m112521/useless-machines/imgs/a4988.jpeg

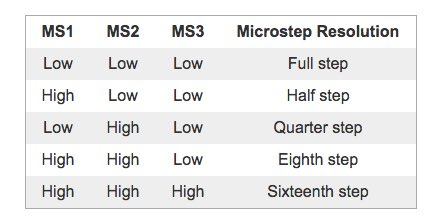
imgs/a4988.jpeg
