m112521/useless-machines/imgs/microstep-config.jpg

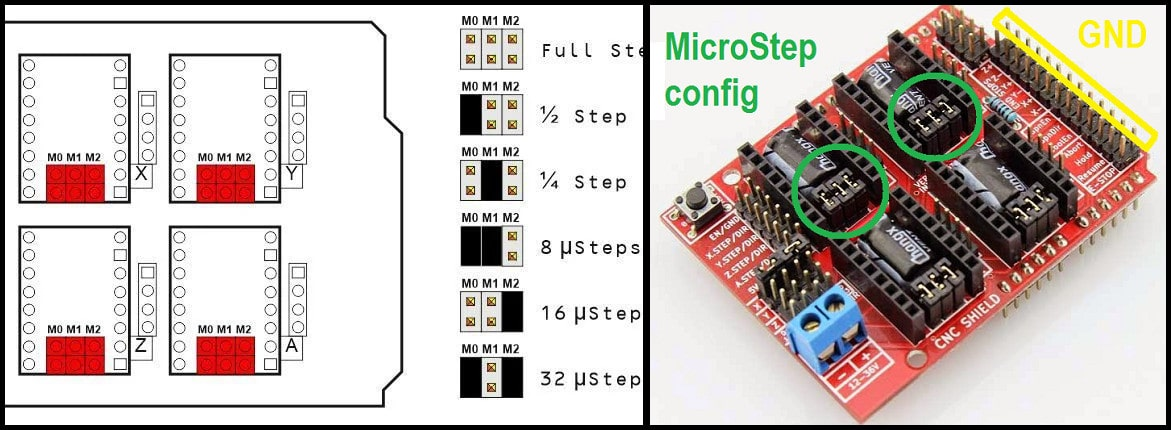
imgs/microstep-config.jpg
