m112521/useless-machines/STL/Z-axis/ToolHolder_v01.stl

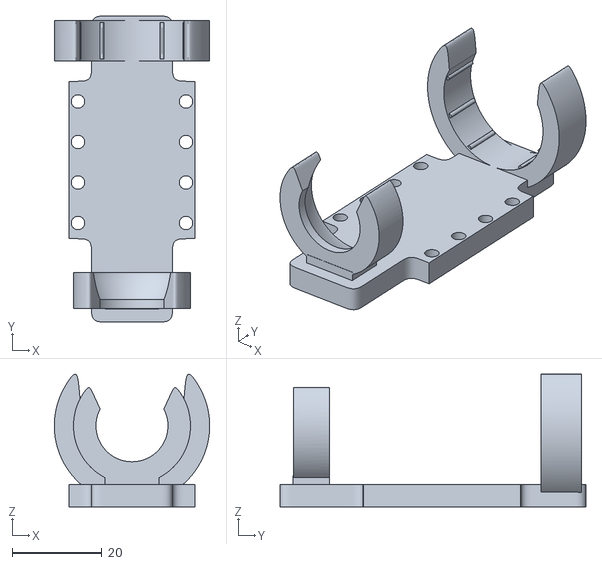
[picture p21: CAD file, 2024-03-12]
STL/Z-axis/ToolHolder_v01.stl
34.5 x 68.0 x 29.5
