m112521/useless-machines/CAD/baseD3.dxf

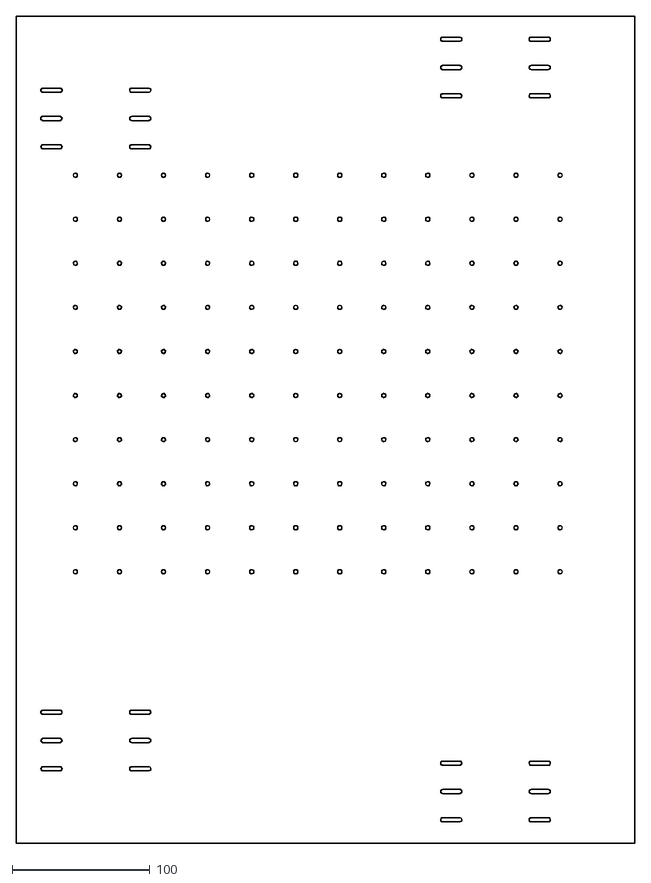
[picture p22: CAD file, 2024-06-20]
CAD/baseD3.dxf
449.3 x 600.6
