m112521/useless-machines/KIT/racks.dxf

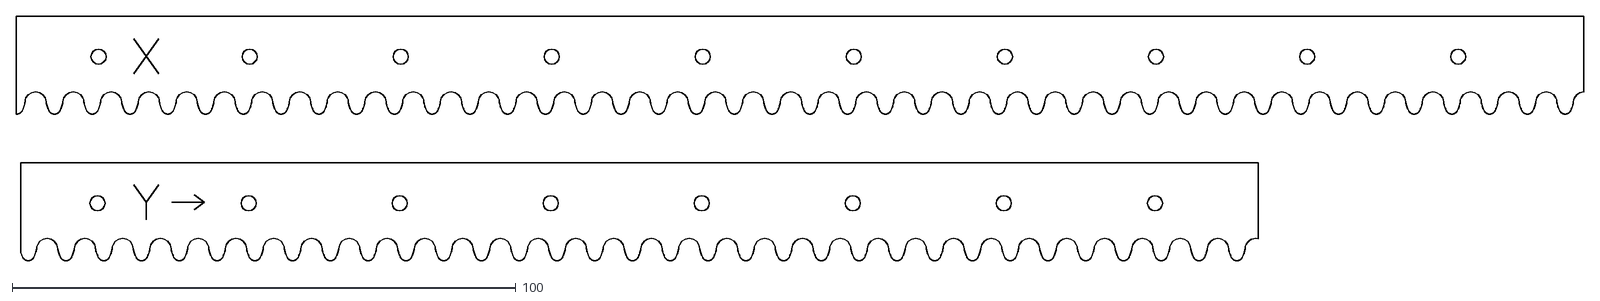
[picture p23: CAD file, 2024-05-28]
KIT/racks.dxf
311.4 x 48.5
