m112521/useless-machines/STEP/carrige_bread_t18_w50.stp

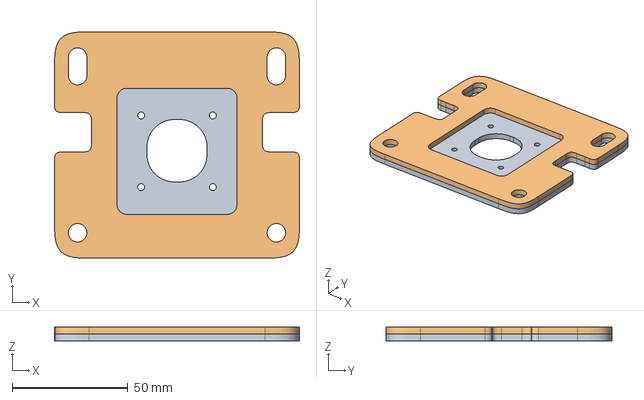
[picture p24: CAD file, 2026-01-15]
STEP/carrige_bread_t18_w50.stp
106.0 x 97.9 x 6.00 mm
