m112521/useless-machines/STL/endstopHolderVX.stl

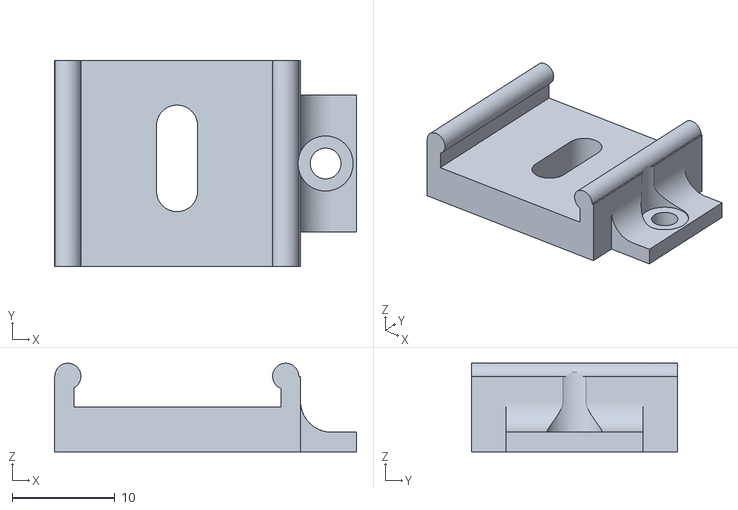
[picture p25: CAD file, 2024-07-02]
STL/endstopHolderVX.stl
29.3 x 20.0 x 8.61
