m112521/useless-machines/STL/Z-axis/StepperHolders.stl

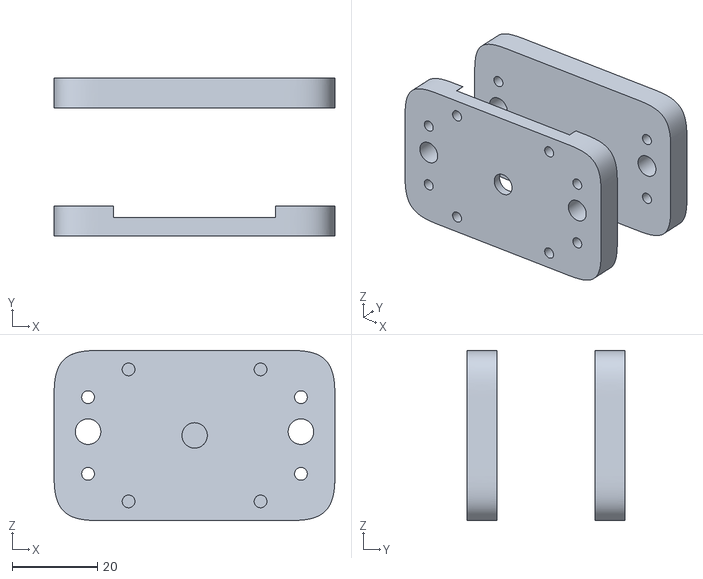
[picture p26: CAD file, 2024-03-07]
STL/Z-axis/StepperHolders.stl
66.0 x 37.0 x 40.0
