m112521/useless-machines/CAD/baseD6.dxf

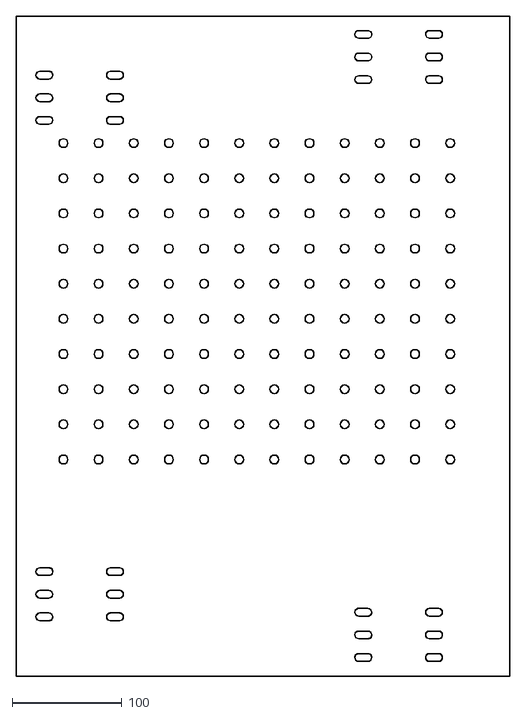
[picture p27: CAD file, 2024-06-20]
CAD/baseD6.dxf
449.3 x 600.6
