m112521/useless-machines/STEP/carrige_cheese_t12_w50.stp

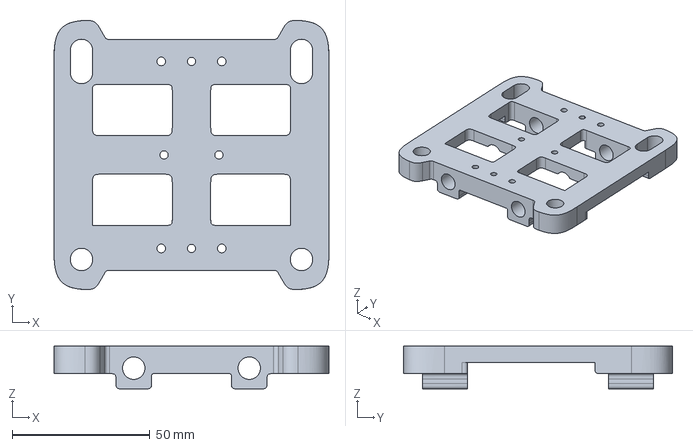
[picture p28: CAD file, 2026-01-15]
STEP/carrige_cheese_t12_w50.stp
100.0 x 97.9 x 15.5 mm
