m112521/useless-machines/STL/endstopHolder_v2.stl

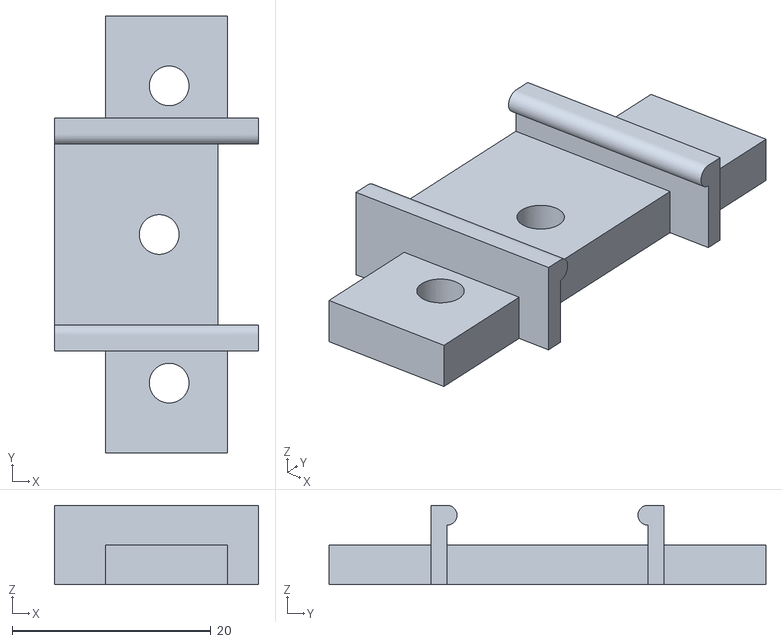
[picture p29: CAD file, 2024-06-11]
STL/endstopHolder_v2.stl
20.5 x 44.0 x 8.00
