m112521/useless-machines/CAD/cameraBeam.dxf

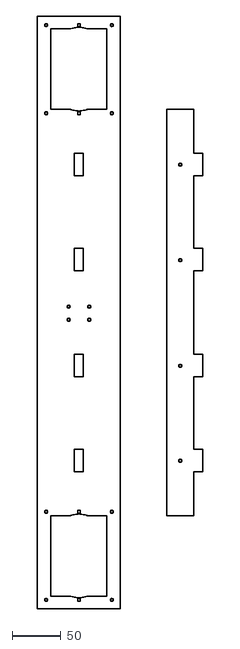
[picture p30: CAD file, 2024-06-07]
CAD/cameraBeam.dxf
169.0 x 605.0
