m112521/useless-machines/STL/foot.stl

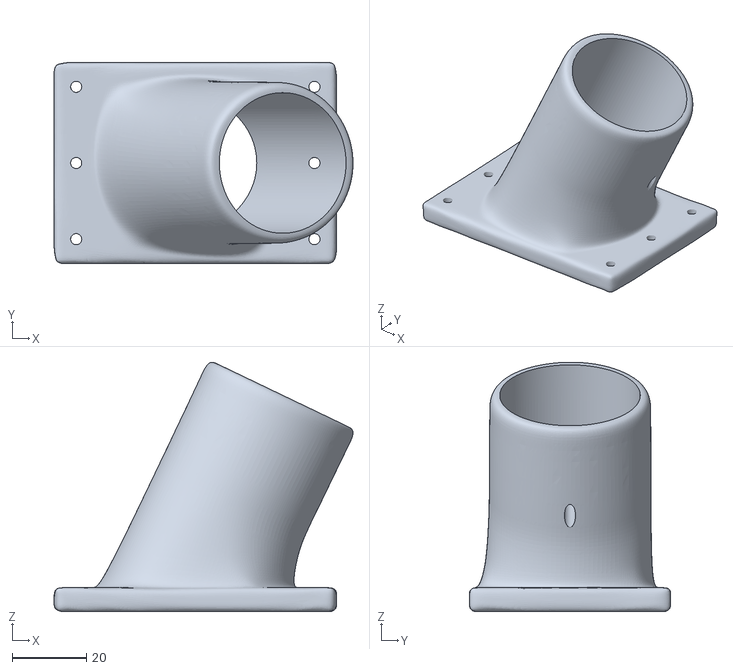
[picture p32: CAD file, 2024-05-28]
STL/foot.stl
80.8 x 54.4 x 67.4
