m112521/useless-machines/STL/Z-axis/RailHolderTop.stl

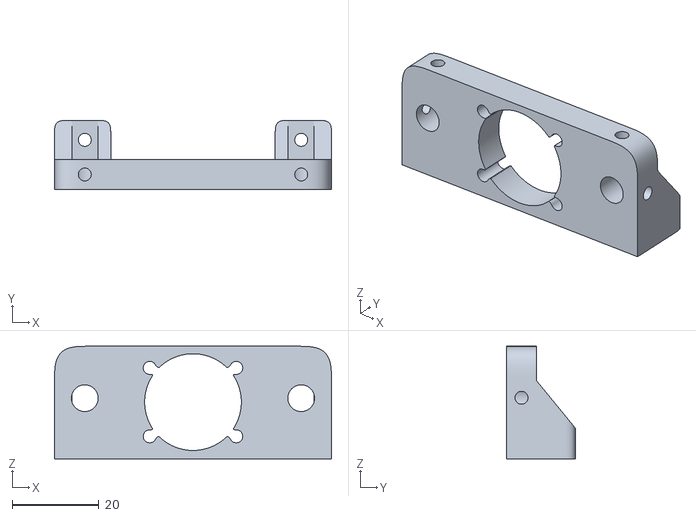
[picture p33: CAD file, 2024-03-01]
STL/Z-axis/RailHolderTop.stl
64.0 x 16.0 x 26.0
