m112521/useless-machines/CAD/flexicamRail.dxf

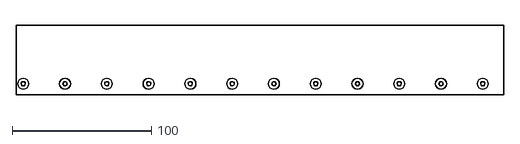
[picture p34: CAD file, 2023-10-10]
CAD/flexicamRail.dxf
350.0 x 50.0
