m112521/useless-machines/STEP/carrige_cheese_t18_w50.stp

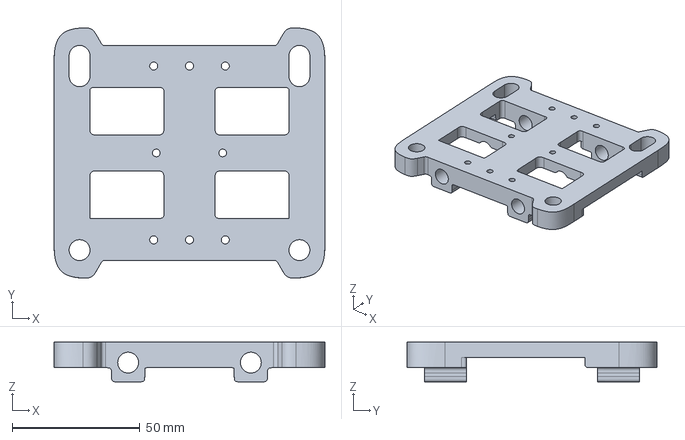
[picture p35: CAD file, 2026-01-15]
STEP/carrige_cheese_t18_w50.stp
106.0 x 97.9 x 15.5 mm
