m112521/useless-machines/STL/axisSupport_v2.stl

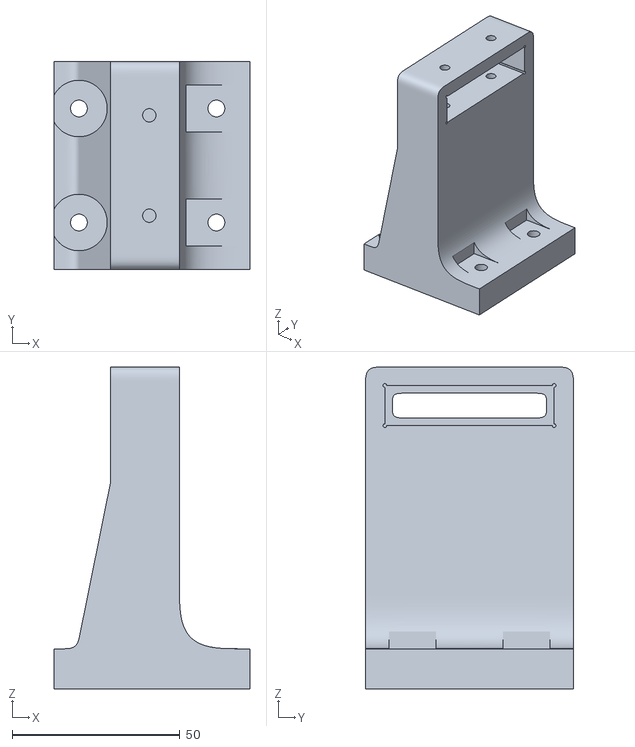
[picture p36: CAD file, 2024-04-23]
STL/axisSupport_v2.stl
58.4 x 62.0 x 96.0
