m112521/useless-machines/STL/Z-axis/Plate.stl

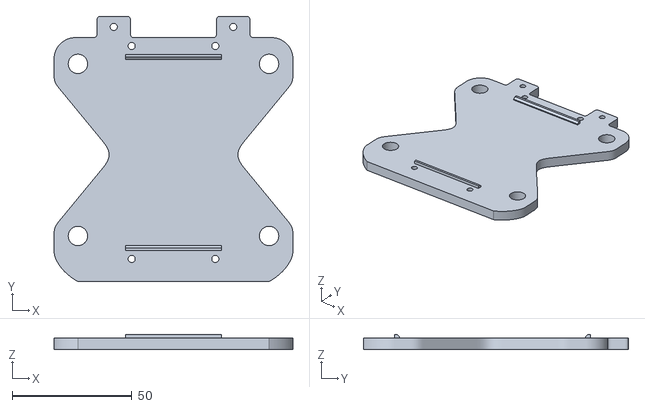
[picture p37: CAD file, 2024-03-01]
STL/Z-axis/Plate.stl
100.0 x 111.0 x 6.48
