m112521/useless-machines/STEP/carrige_endstopHolder.stp

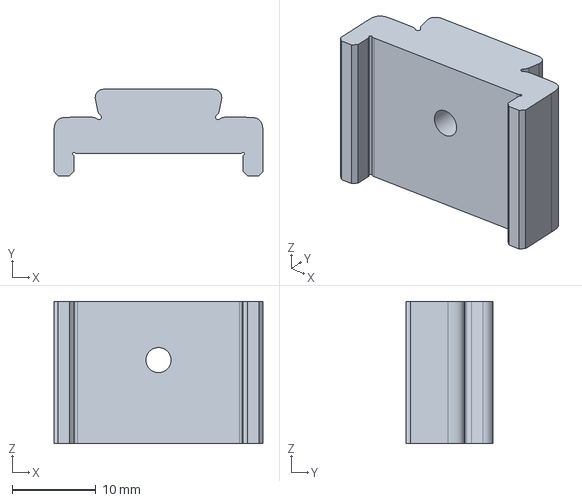
[picture p38: CAD file, 2026-01-15]
STEP/carrige_endstopHolder.stp
25.0 x 10.3 x 17.0 mm
