m112521/useless-machines/STL/bottomBearingSpacers_v2.stl

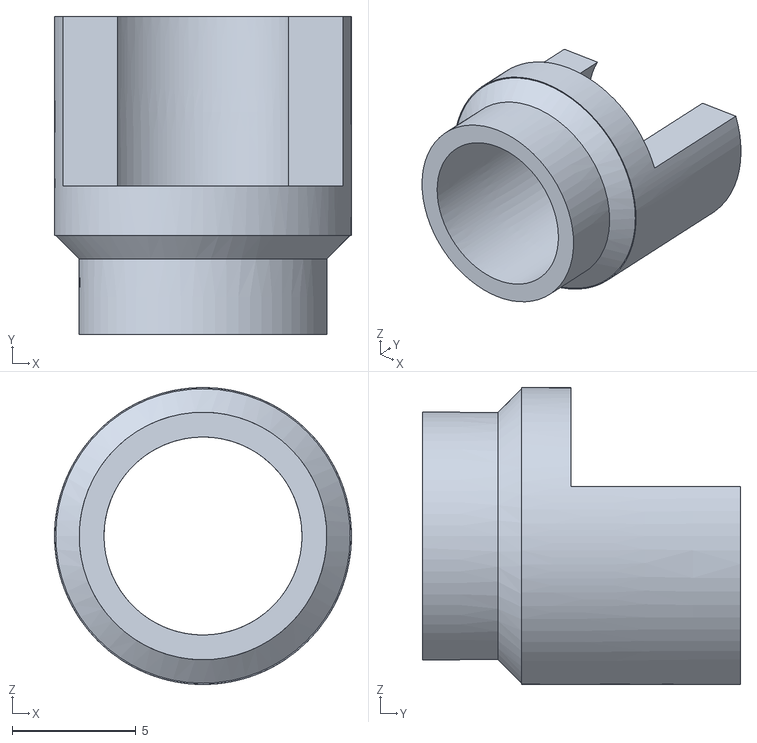
[picture p39: CAD file, 2024-04-23]
STL/bottomBearingSpacers_v2.stl
12.0 x 12.9 x 12.0
