m112521/useless-machines/STL/Z-axis/RailHolderBottom.stl

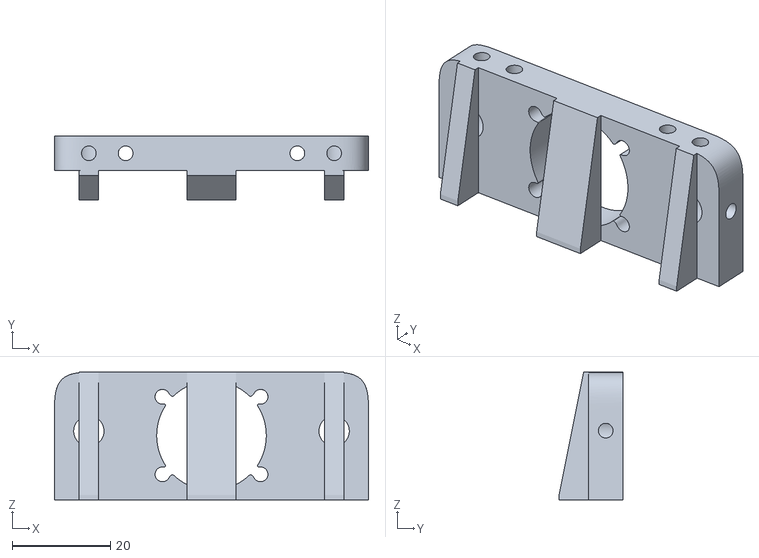
[picture p40: CAD file, 2024-03-01]
STL/Z-axis/RailHolderBottom.stl
64.0 x 13.0 x 26.0
