m112521/useless-machines/STEP/carrige_jam_t18_w50.stp

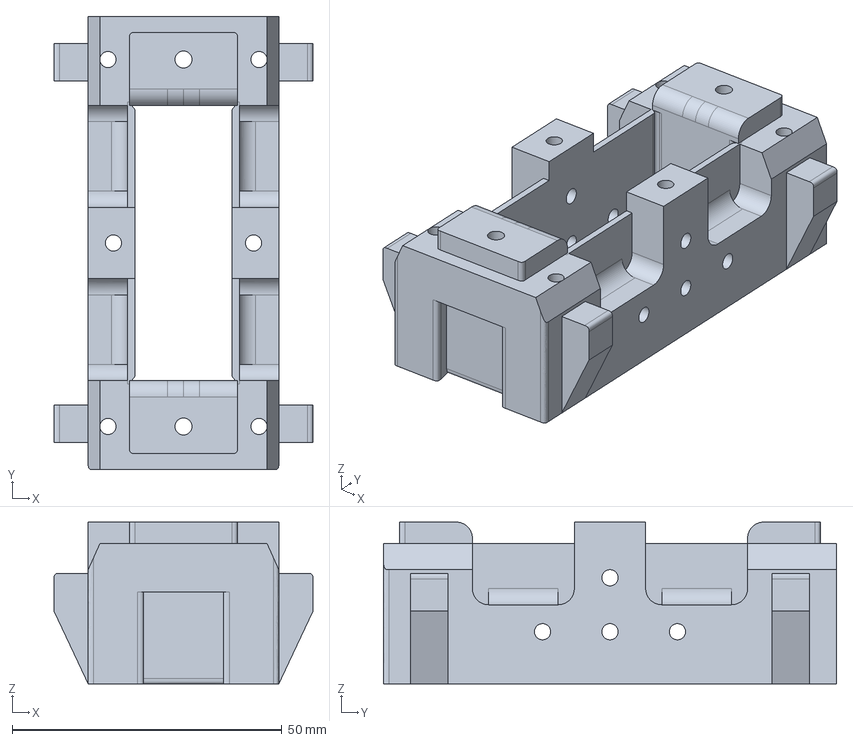
[picture p41: CAD file, 2026-01-15]
STEP/carrige_jam_t18_w50.stp
48.0 x 84.0 x 30.0 mm
