m112521/useless-machines/STL/bearingSpacer.stl

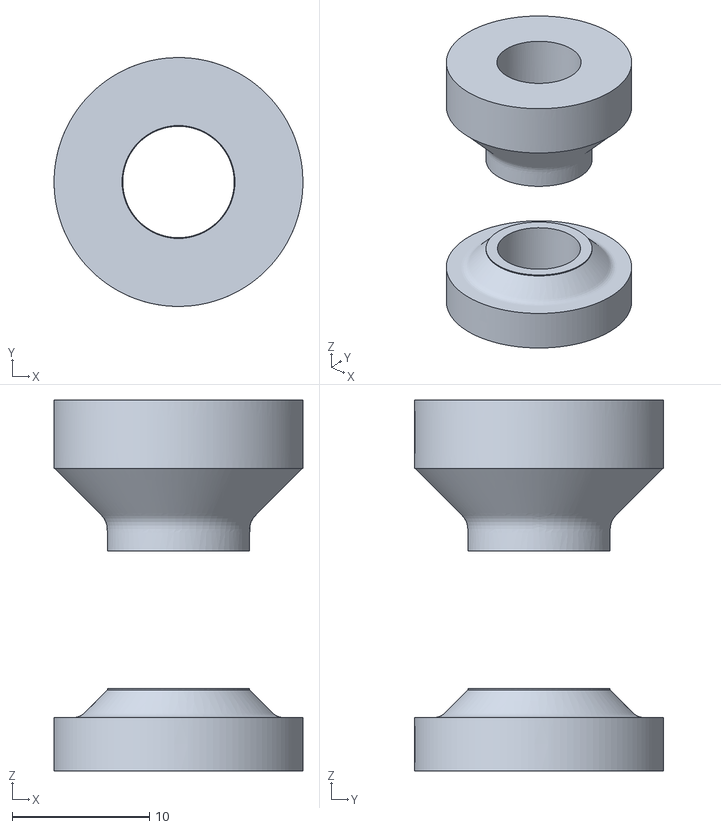
[picture p42: CAD file, 2023-11-07]
STL/bearingSpacer.stl
18.1 x 18.1 x 27.0
