m112521/useless-machines/STL/Z-axis/RailHolderTop_spacered.stl

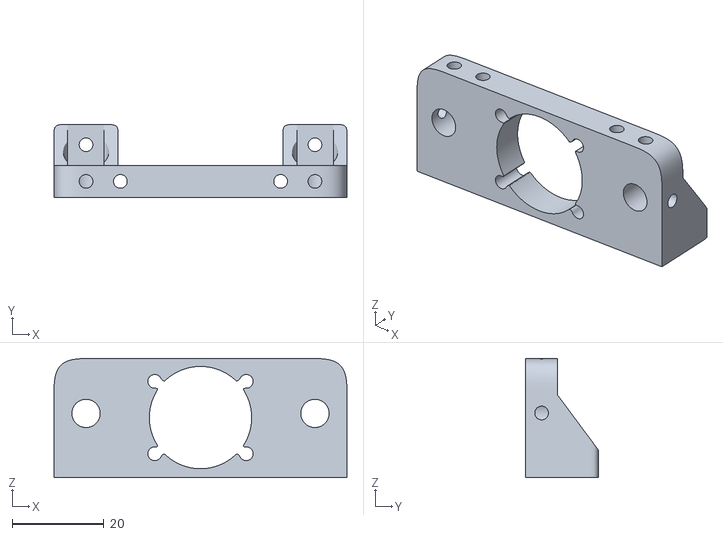
[picture p43: CAD file, 2024-03-01]
STL/Z-axis/RailHolderTop_spacered.stl
64.0 x 15.9 x 26.0
