m112521/useless-machines/STL/pinion.stl

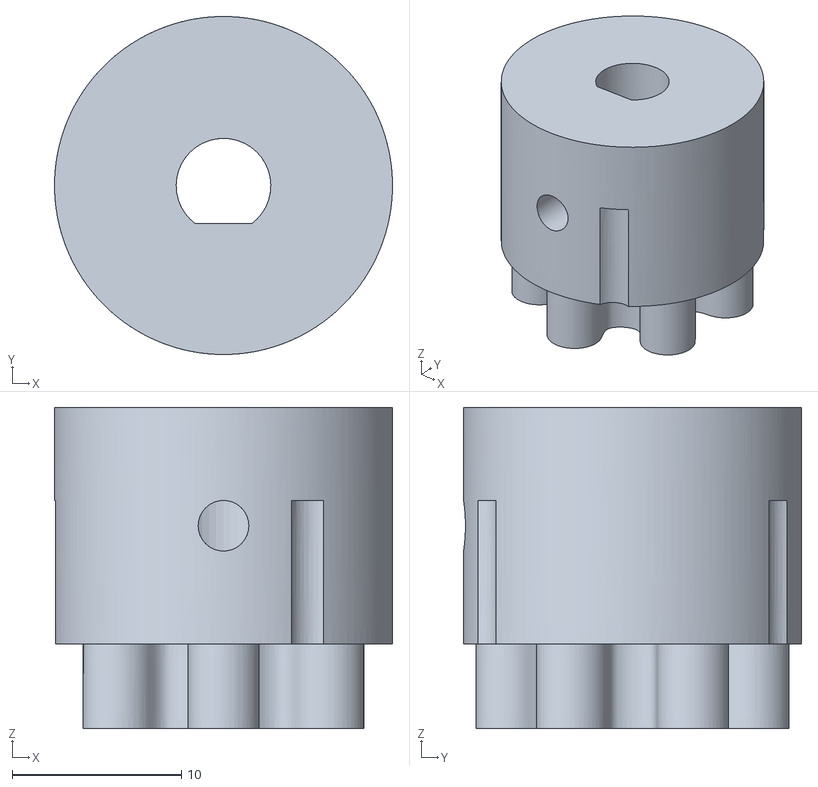
[picture p44: CAD file, 2023-11-07]
STL/pinion.stl
20.0 x 20.0 x 19.0
