m112521/useless-machines/STL/axisSupportStatic.stl

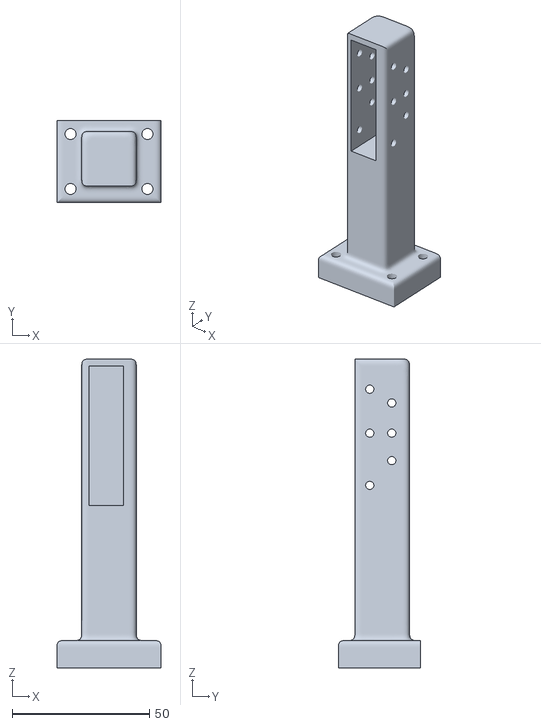
[picture p45: CAD file, 2023-11-07]
STL/axisSupportStatic.stl
38.0 x 30.0 x 112.5
