m112521/useless-machines/STL/perpAxisHolderArched.stl

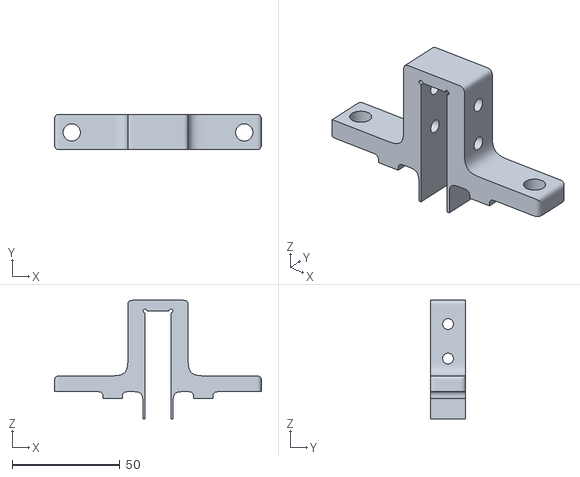
[picture p46: CAD file, 2023-11-07]
STL/perpAxisHolderArched.stl
96.0 x 16.4 x 55.0
