m112521/useless-machines/STL/carrigeBracket.stl

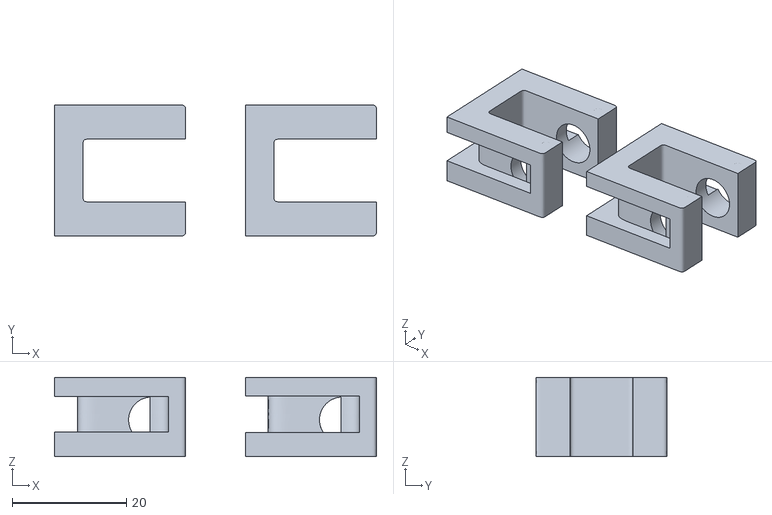
[picture p47: CAD file, 2023-10-10]
STL/carrigeBracket.stl
56.5 x 23.0 x 13.9
