m112521/useless-machines/STL/BottomCarrigePLA2.stl

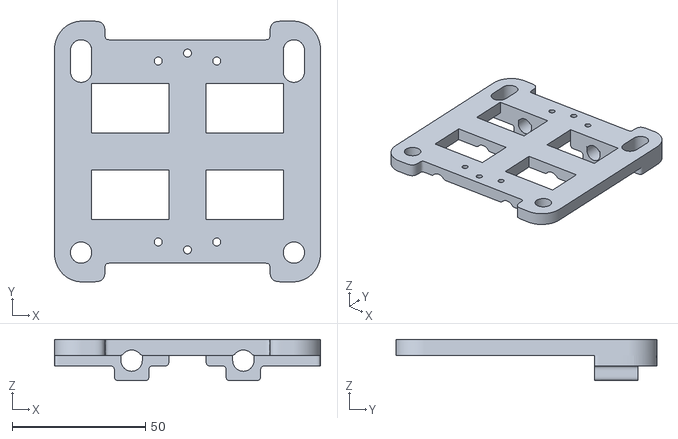
[picture p48: CAD file, 2023-10-10]
STL/BottomCarrigePLA2.stl
100.0 x 98.0 x 15.5
