m112521/useless-machines/STL/nemaHolder.stl

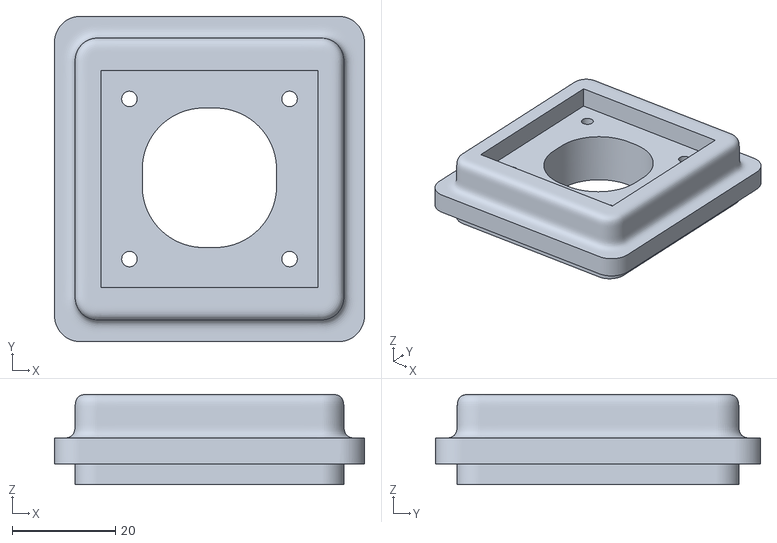
[picture p49: CAD file, 2023-10-10]
STL/nemaHolder.stl
60.0 x 62.9 x 17.5
