m112521/useless-machines/STL/BottomCarrigePLA3.stl

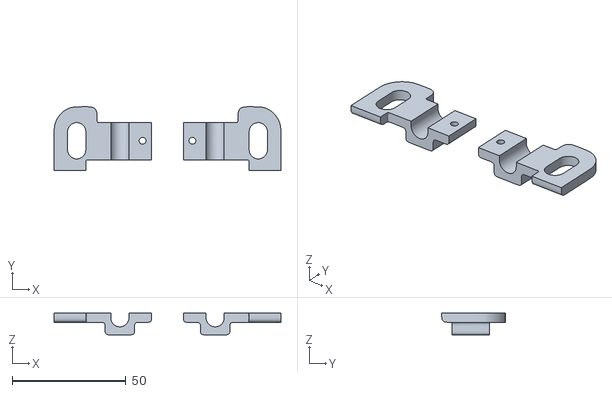
[picture p50: CAD file, 2023-10-10]
STL/BottomCarrigePLA3.stl
100.0 x 28.0 x 9.52
