m112521/useless-machines/STL/BottomCarrigePLA.stl

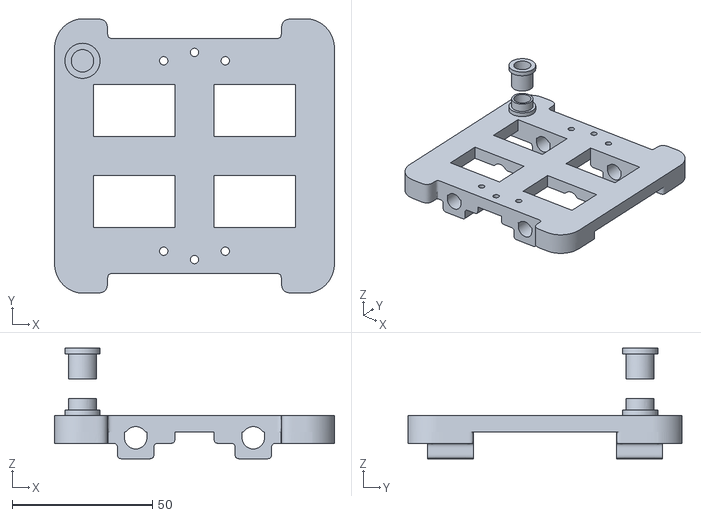
[picture p51: CAD file, 2023-10-10]
STL/BottomCarrigePLA.stl
100.0 x 98.0 x 39.5
