m112521/useless-machines/imgs/diodeLaser-setup.jpg

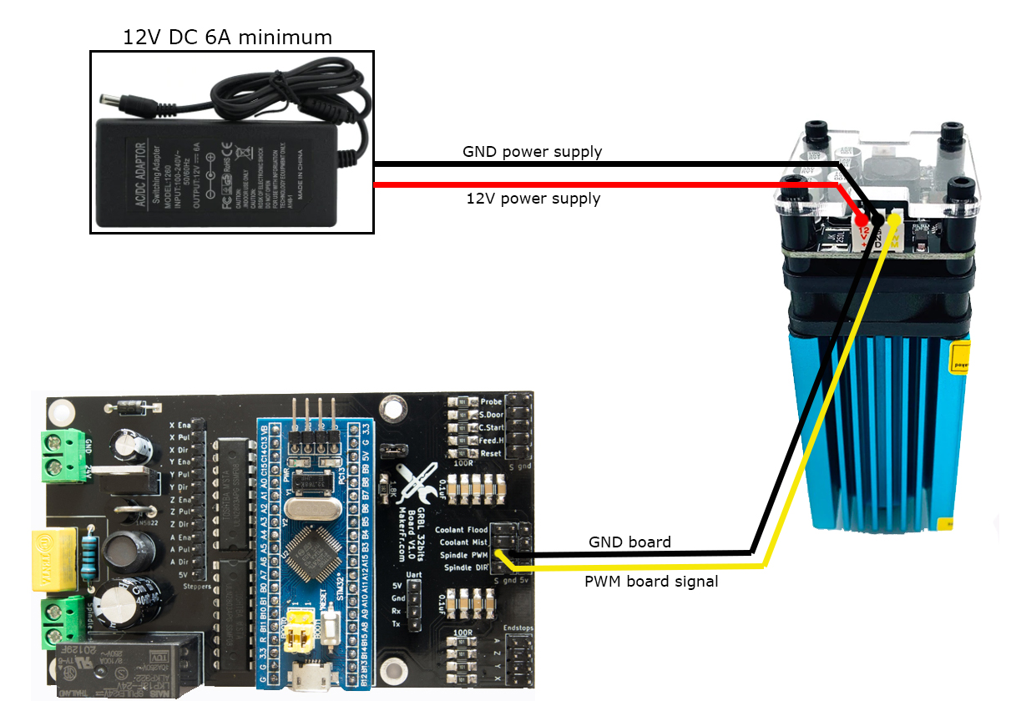
imgs/diodeLaser-setup.jpg
