m112521/useless-machines/imgs/relay-setup2.PNG

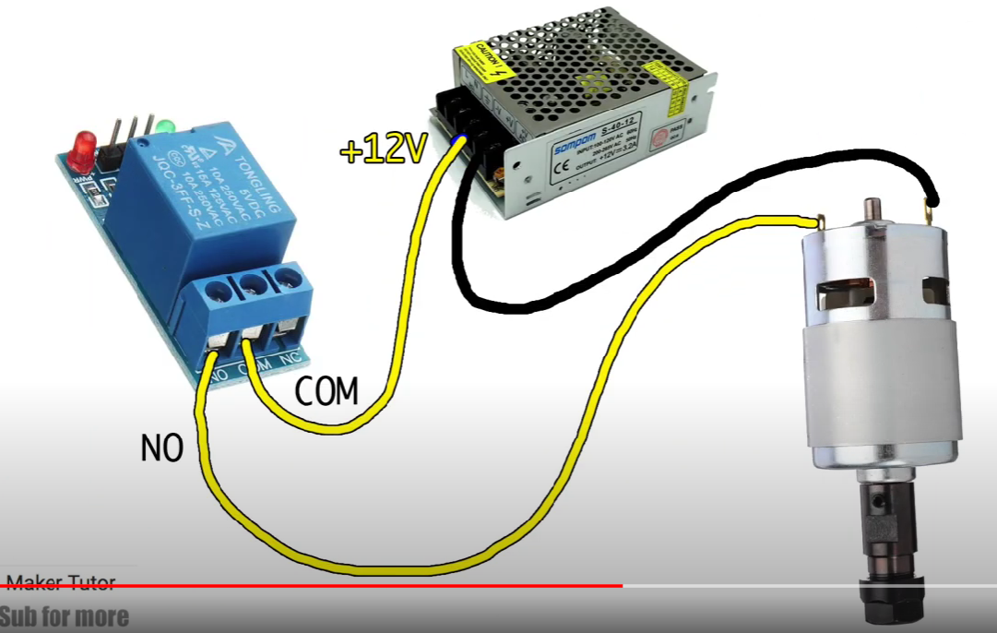
imgs/relay-setup2.PNG
