m112521/useless-machines/imgs/wiring.PNG

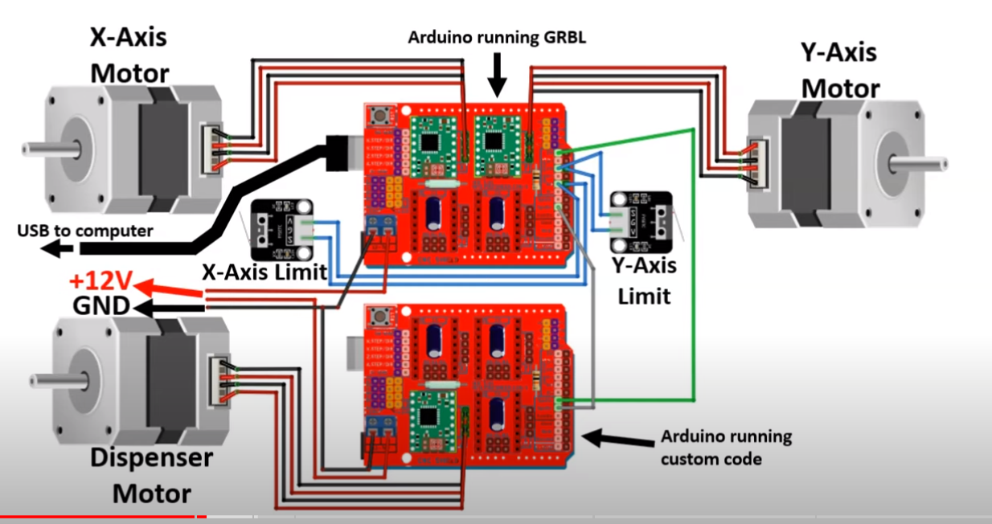
imgs/wiring.PNG
