m112521/useless-machines/src/undistort.py

import numpy as np
import cv2 as cv
import glob



################ FIND CHESSBOARD CORNERS - OBJECT POINTS AND IMAGE POINTS #############################

chessboardSize = (9,6)
frameSize = (640,480)



# termination criteria
criteria = (cv.TERM_CRITERIA_EPS + cv.TERM_CRITERIA_MAX_ITER, 30, 0.001)


# prepare object points, like (0,0,0), (1,0,0), (2,0,0) ....,(6,5,0)
objp = np.zeros((chessboardSize[0] * chessboardSize[1], 3), np.float32)
objp[:,:2] = np.mgrid[0:chessboardSize[0],0:chessboardSize[1]].T.reshape(-1,2)

size_of_chessboard_squares_mm = 9
objp = objp * size_of_chessboard_squares_mm


# Arrays to store object points and image points from all the images.
objpoints = [] # 3d point in real world space
imgpoints = [] # 2d points in image plane.


images = glob.glob('imgs/calib/*.png')  # /imgs/calib/*.png
print(images)

for image in images:

    img = cv.imread(image)
    gray = cv.cvtColor(img, cv.COLOR_BGR2GRAY)

    # hsv = cv.cvtColor(img, cv.COLOR_BGR2HSV)
    # lower = np.array([75, 0, 189], np.uint8)
    # upper = np.array([180, 116, 255], np.uint8)
    # mask = cv.inRange(hsv, lower, upper)


    # Find the chess board corners
    ret, corners = cv.findChessboardCorners(gray, chessboardSize, None)

    # If found, add object points, image points (after refining them)
    if ret == True:
        print("Yes")
        objpoints.append(objp)
        corners2 = cv.cornerSubPix(gray, corners, (11,11), (-1,-1), criteria)
        imgpoints.append(corners)

        # Draw and display the corners
        cv.drawChessboardCorners(img, chessboardSize, corners2, ret)
        cv.imshow('img', img)
        cv.waitKey(500)


cv.destroyAllWindows()



############## CALIBRATION #######################################################

ret, cameraMatrix, dist, rvecs, tvecs = cv.calibrateCamera(objpoints, imgpoints, frameSize, None, None)
savedir = 'params/'
print("Camera Matrix")
print(cameraMatrix)
np.save(savedir+'cameraMatrix.npy', cameraMatrix)

print("Distortion Coeff")
print(dist)
np.save(savedir + 'dist.npy', dist)

print("r vecs")
print(rvecs)

print("t vecs")
print(tvecs)

############## UNDISTORTION #####################################################

img = cv.imread('imgs/calib/0.png')
h,  w = img.shape[:2]
newCameraMatrix, roi = cv.getOptimalNewCameraMatrix(cameraMatrix, dist, (w,h), 1, (w,h))



# Undistort
dst = cv.undistort(img, cameraMatrix, dist, None, newCameraMatrix)

# crop the image
x, y, w, h = roi
dst = dst[y:y+h, x:x+w]
cv.imwrite('imgs/calib/caliResult1.png', dst)



# Undistort with Remapping
mapx, mapy = cv.initUndistortRectifyMap(cameraMatrix, dist, None, newCameraMatrix, (w,h), 5)
dst = cv.remap(img, mapx, mapy, cv.INTER_LINEAR)

# crop the image
x, y, w, h = roi
dst = dst[y:y+h, x:x+w]
cv.imwrite('imgs/calib/caliResult2.png', dst)




# Reprojection Error
mean_error = 0

for i in range(len(objpoints)):
    imgpoints2, _ = cv.projectPoints(objpoints[i], rvecs[i], tvecs[i], cameraMatrix, dist)
    error = cv.norm(imgpoints[i], imgpoints2, cv.NORM_L2)/len(imgpoints2)
    mean_error += error

print( "total error: {}".format(mean_error/len(objpoints)) )
