m112521/useless-machines/src/gen_aruco.py

import numpy as np
import cv2, PIL
from cv2 import aruco
import matplotlib.pyplot as plt
import matplotlib as mpl
import pandas as pd

aruco_dict = aruco.Dictionary_get(aruco.DICT_4X4_50)

fig = plt.figure()
nx = 4
ny = 3
for i in range(1, nx*ny+1):
    ax = fig.add_subplot(ny,nx, i)
    img = aruco.drawMarker(aruco_dict,i, 700)
    plt.imshow(img, cmap = mpl.cm.gray, interpolation = "nearest")
    ax.axis("off")

plt.savefig("markers4x4.jpeg")
plt.show()
