m112521/useless-machines/src/cnc_a4988/test_serial.py

import serial
import time
from threading import Event

BAUD_RATE = 115200

def remove_comment(string):
    if (string.find(';') == -1):
        return string
    else:
        return string[:string.index(';')]


def remove_eol_chars(string):
    # removed \n or traling spaces
    return string.strip()


def send_wake_up(ser):
    # Wake up
    # Hit enter a few times to wake the Printrbot
    ser.write(str.encode("\r\n\r\n"))
    time.sleep(2)   # Wait for Printrbot to initialize
    ser.flushInput()  # Flush startup text in serial input

def wait_for_movement_completion(ser,cleaned_line):

    Event().wait(1)

    if cleaned_line != '$X' or '$$':

        idle_counter = 0

        while True:

            # Event().wait(0.01)
            ser.reset_input_buffer()
            command = str.encode('?' + '\n')
            ser.write(command)
            grbl_out = ser.readline() 
            grbl_response = grbl_out.strip().decode('utf-8')

            if grbl_response != 'ok':

                if grbl_response.find('Idle') > 0:
                    idle_counter += 1

            if idle_counter > 10:
                break
    return


def stream_gcode(GRBL_port_path,gcode_path):
    # with contect opens file/connection and closes it if function(with) scope is left
    with open(gcode_path, "r") as file, serial.Serial(GRBL_port_path, BAUD_RATE) as ser:
        send_wake_up(ser)
        for line in file:
            # cleaning up gcode from file
            cleaned_line = remove_eol_chars(remove_comment(line))
            if cleaned_line:  # checks if string is empty
                print("Sending gcode:" + str(cleaned_line))
                # converts string to byte encoded string and append newline
                command = str.encode(line + '\n')
                ser.write(command)  # Send g-code

                wait_for_movement_completion(ser,cleaned_line)

                grbl_out = ser.readline()  # Wait for response with carriage return
                print(" : " , grbl_out.strip().decode('utf-8'))

                
        
        print('End of gcode')

if __name__ == "__main__":

    GRBL_port_path = 'COM3'
    gcode_path = 'circle.gcode'

    print("USB Port: ", GRBL_port_path)
    print("Gcode file: ", gcode_path)
    stream_gcode(GRBL_port_path,gcode_path)

    print('EOF')
